fima85/RemoteControl/misc/arduino/RingCap.SLDPRT

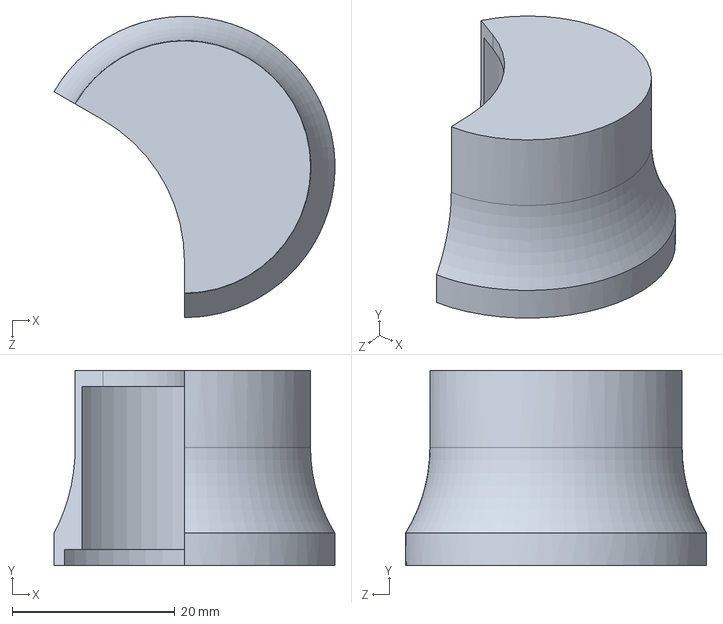
[picture p17: CAD file, 2017-01-29]
misc/arduino/RingCap.SLDPRT
34.5 x 24.0 x 37.0 mm
