fima85/RemoteControl/misc/ACS Joystick sketch/ServoHolder.SLDPRT

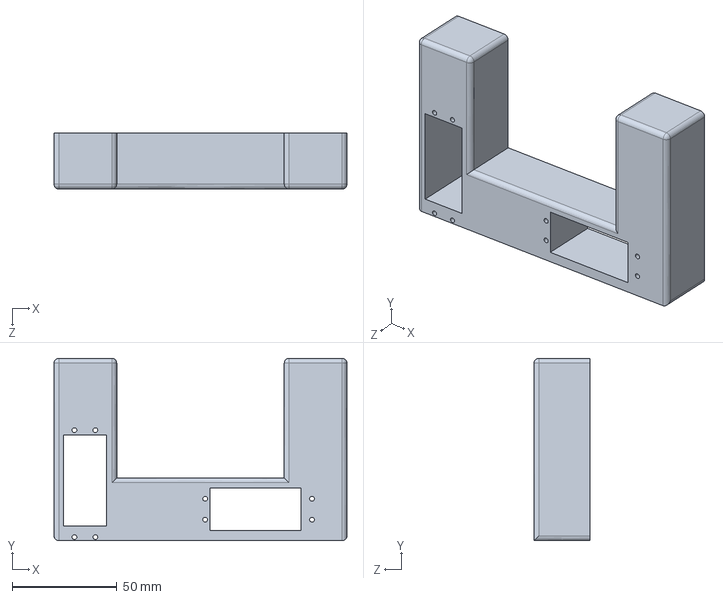
[picture p18: CAD file, 2017-01-09]
misc/ACS Joystick sketch/ServoHolder.SLDPRT
140.0 x 87.1 x 26.8 mm
