fima85/RemoteControl/misc/arduino/coverbox.SLDPRT

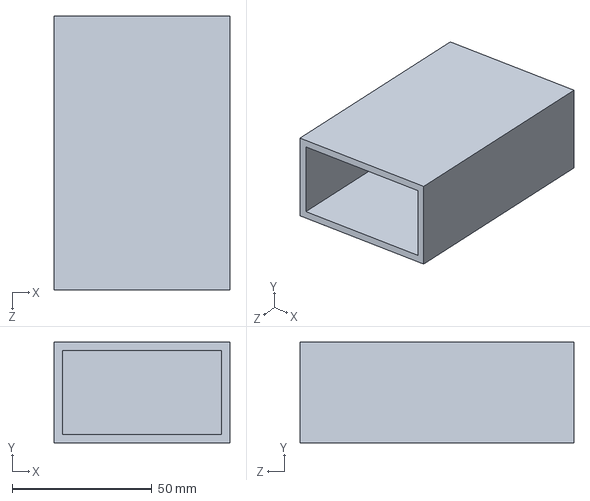
[picture p19: CAD file, 2017-01-29]
misc/arduino/coverbox.SLDPRT
63.0 x 36.0 x 98.0 mm
