fima85/RemoteControl/misc/ACS Joystick sketch/bataries.SLDPRT

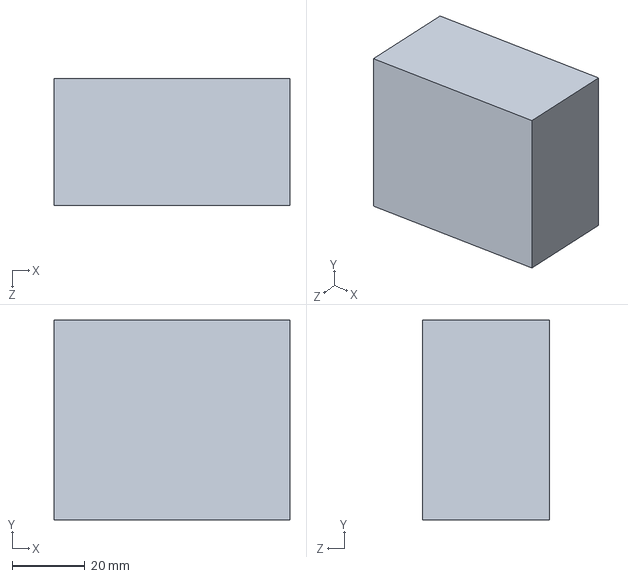
[picture p20: CAD file, 2017-01-09]
misc/ACS Joystick sketch/bataries.SLDPRT
65.0 x 55.0 x 35.0 mm
