fima85/RemoteControl/misc/arduino/Joystick.SLDPRT

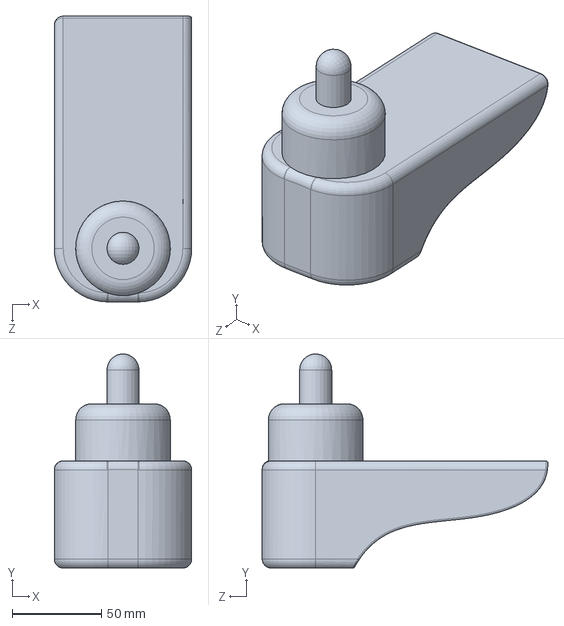
[picture p21: CAD file, 2017-01-09]
misc/arduino/Joystick.SLDPRT
77.0 x 119.9 x 160.1 mm
