fima85/RemoteControl/misc/ACS Joystick sketch/gumi.SLDPRT

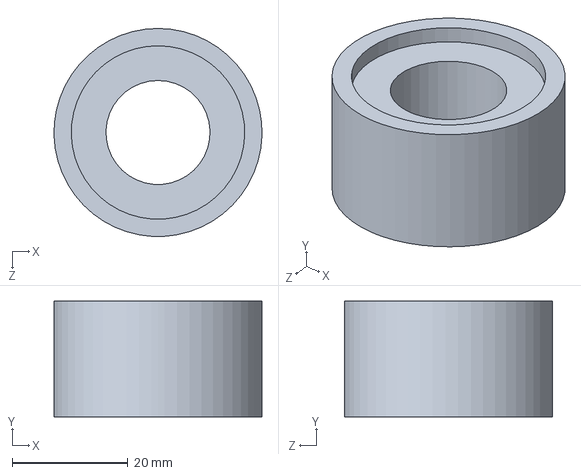
[picture p22: CAD file, 2017-01-09]
misc/ACS Joystick sketch/gumi.SLDPRT
36.0 x 20.0 x 36.0 mm
