fima85/RemoteControl/misc/ACS Joystick sketch/platform_test.SLDPRT

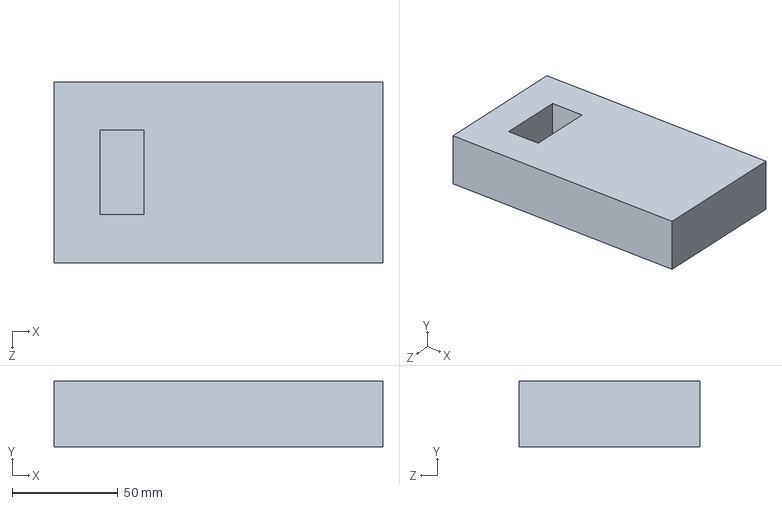
[picture p23: CAD file, 2017-01-09]
misc/ACS Joystick sketch/platform_test.SLDPRT
155.5 x 31.0 x 85.3 mm
