fima85/RemoteControl/misc/ACS Joystick sketch/shoshana.SLDPRT

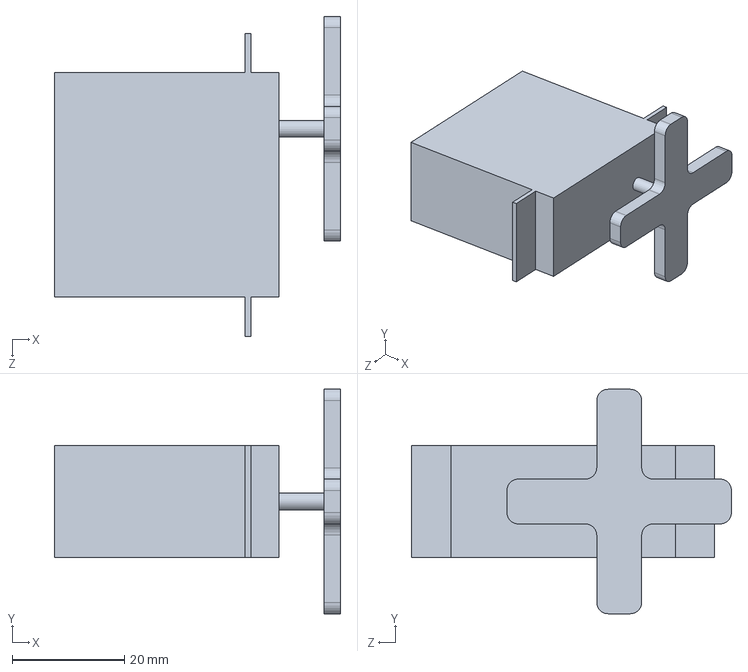
[picture p24: CAD file, 2017-01-09]
misc/ACS Joystick sketch/shoshana.SLDPRT
51.0 x 40.0 x 57.0 mm
