fima85/RemoteControl/misc/ACS Joystick sketch/frame.SLDPRT

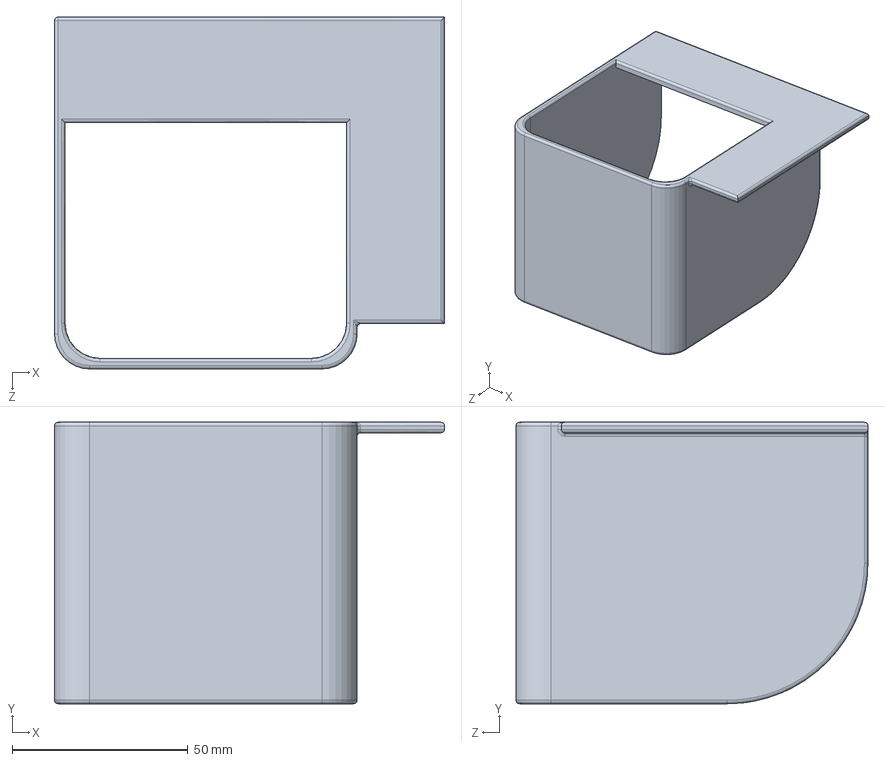
[picture p25: CAD file, 2017-01-09]
misc/ACS Joystick sketch/frame.SLDPRT
110.8 x 80.0 x 100.0 mm
