fima85/RemoteControl/misc/ACS Joystick sketch/electronics.SLDPRT

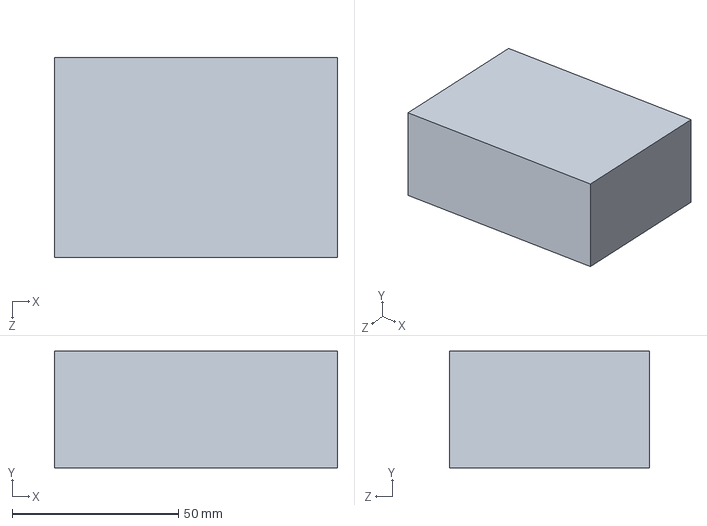
[picture p26: CAD file, 2017-01-09]
misc/ACS Joystick sketch/electronics.SLDPRT
85.0 x 35.0 x 60.0 mm
